FrameworkComputer/RTCRework/outputs/assembly.png

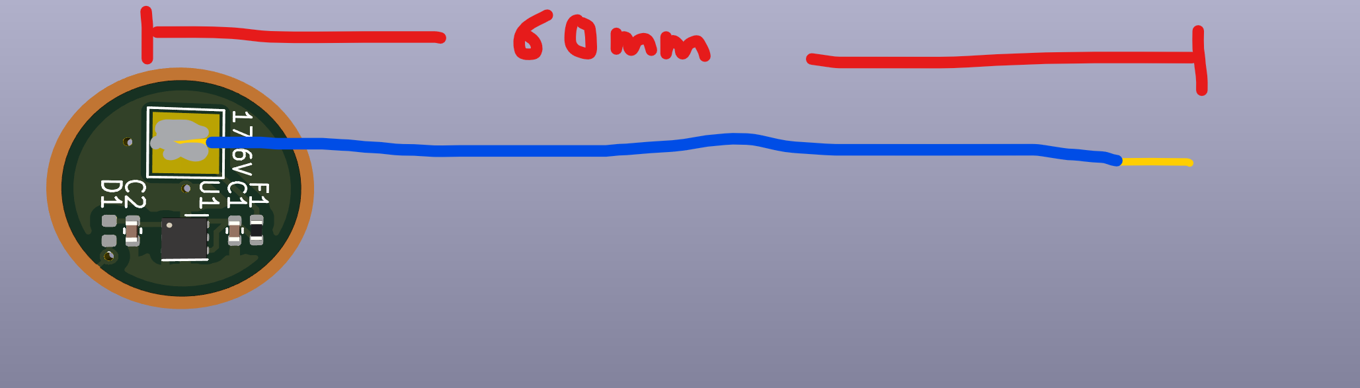
outputs/assembly.png
